kuku-199/Afflatus/HDK/STM32G4/Commander/Commander.pdf

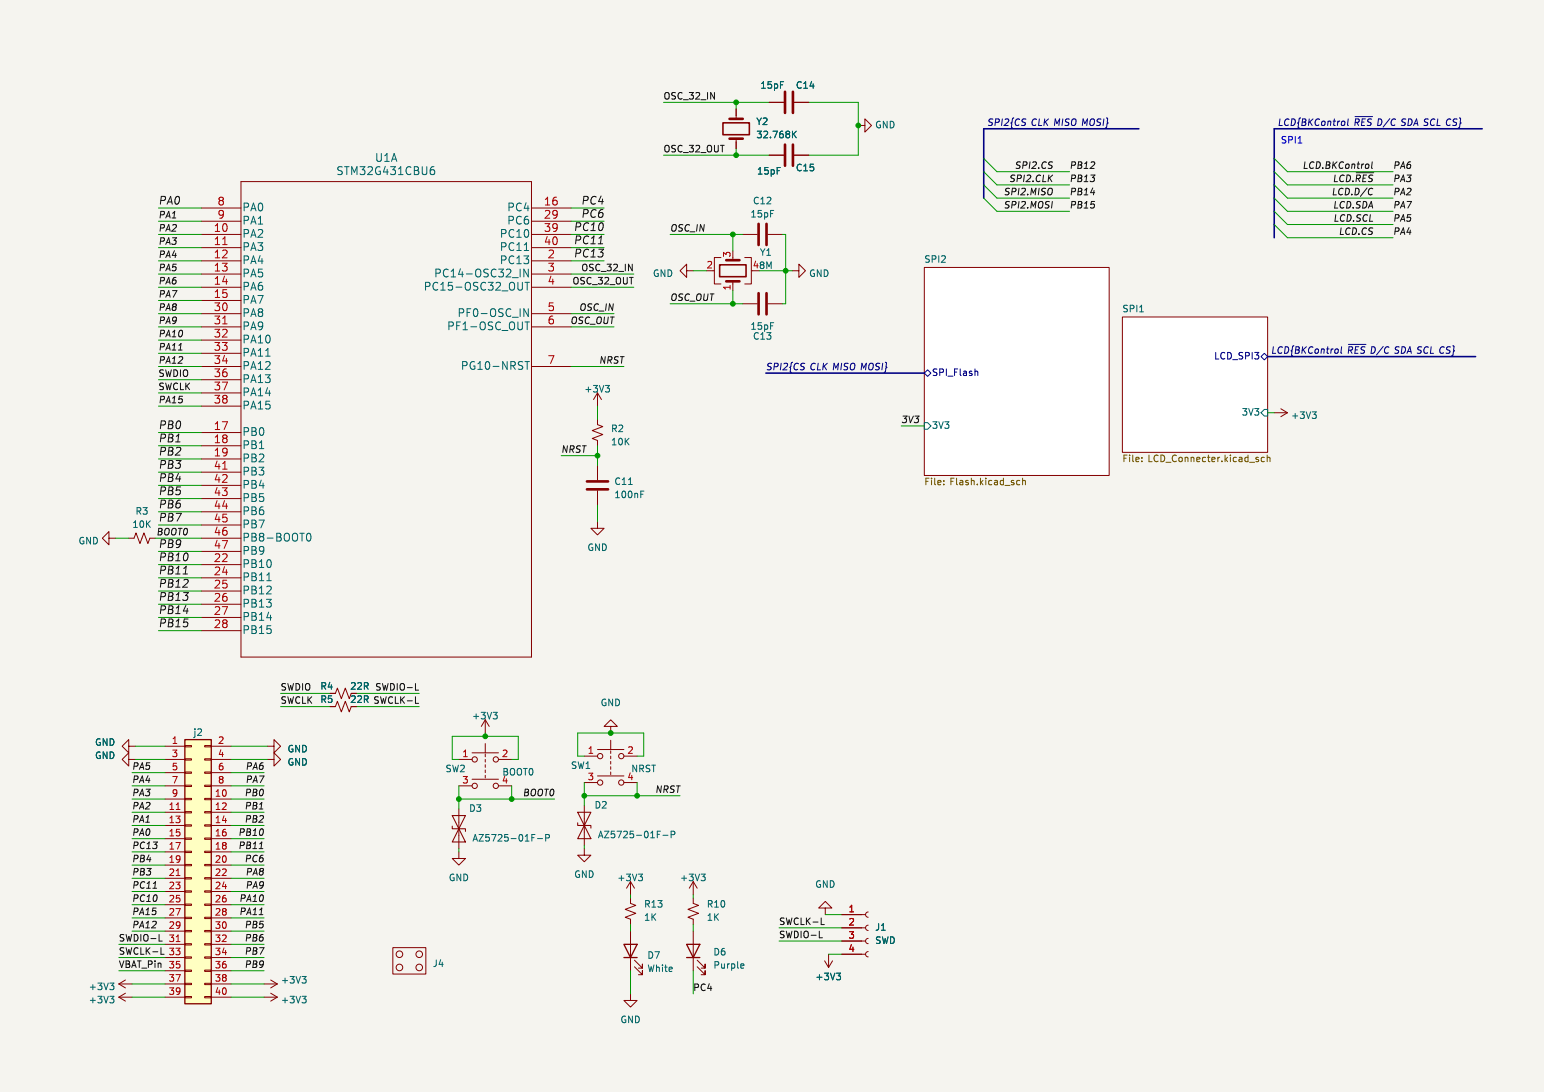
[picture p17: page 1]

LCD{BKControl ~{RES}D/C SDA SCL CS} SWCLK-L

LCD{BKControl ~{RES}D/C SDA SCL CS} PA4 PA5 PA3
SWCLK

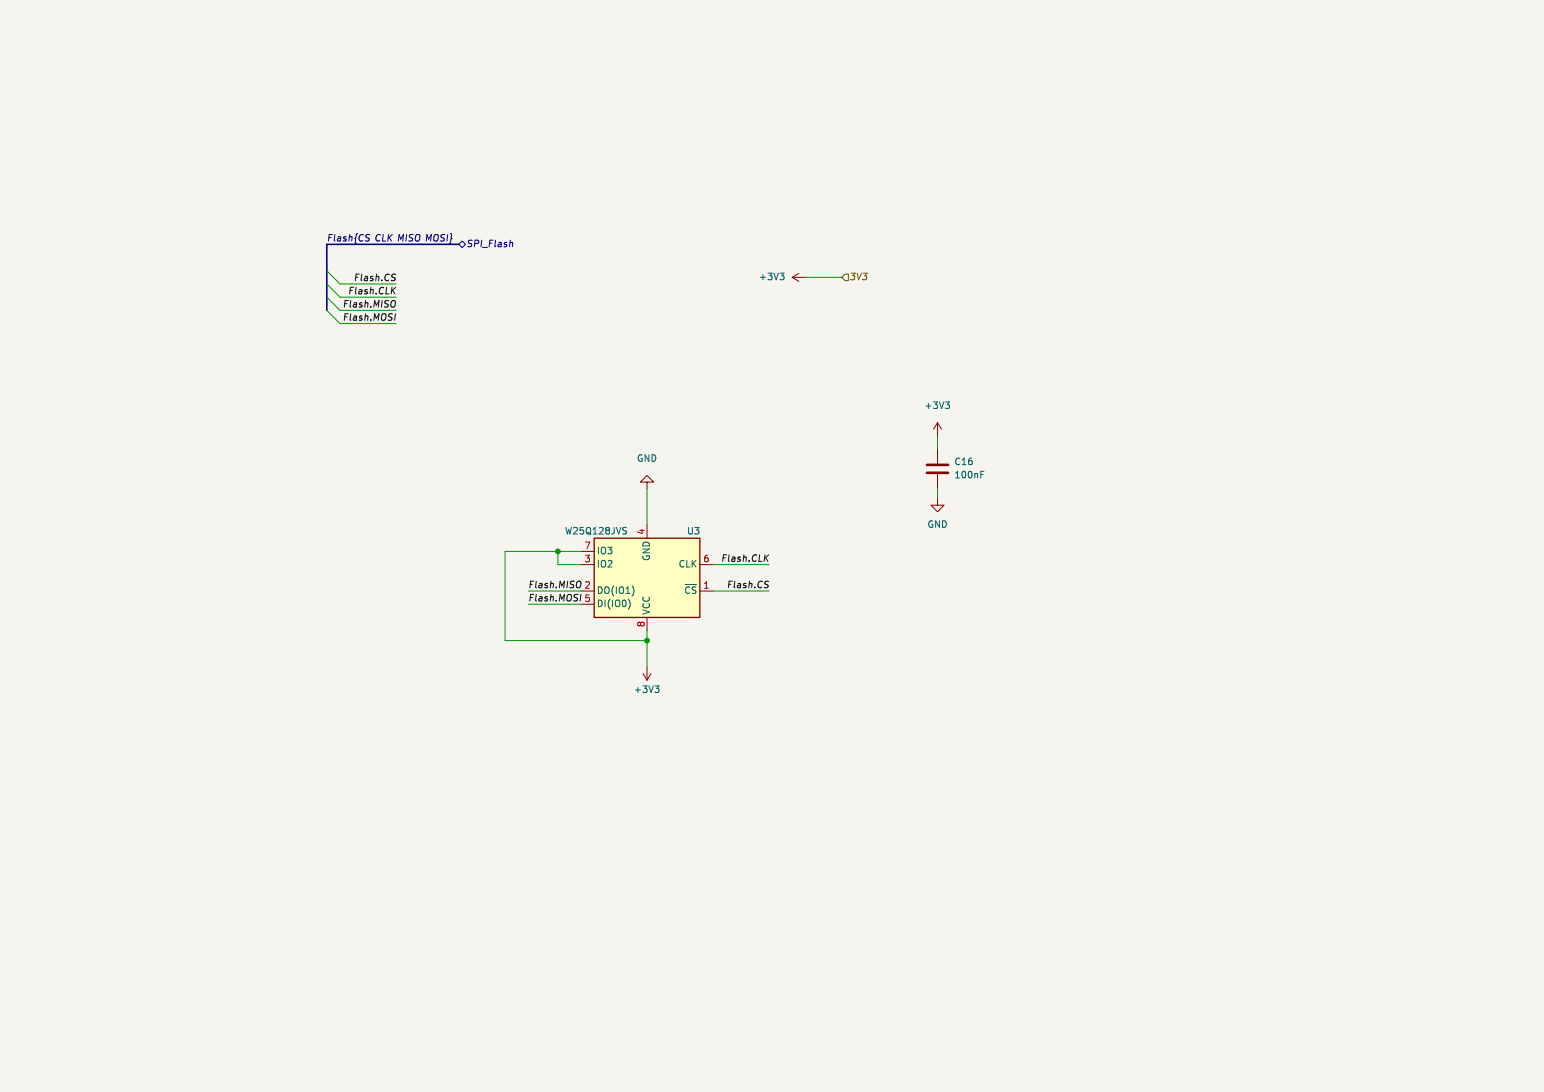
[picture p18: page 2]

Flash{CS CLK MISO MOSI} Flash.MISO

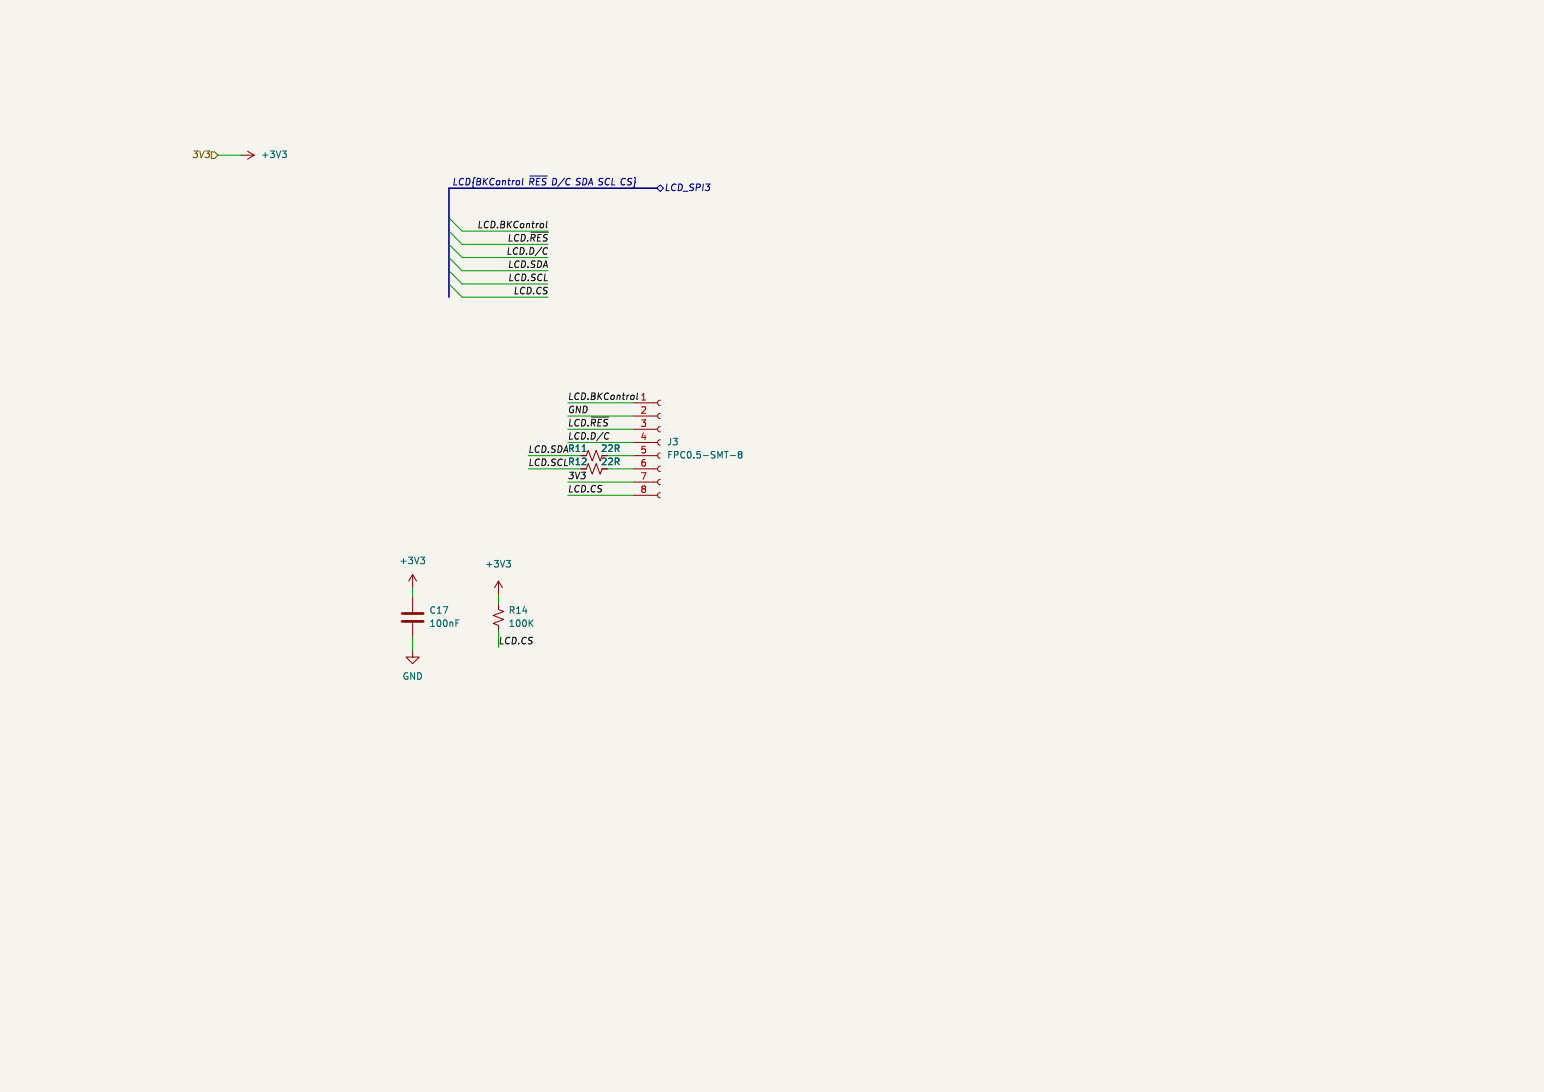
[picture p19: page 3]

LCD.BKControl LCD.SDA
LCD.~{RES} LCD.SCL
LCD.D/C
LCD.SDA
LCD.SCL
LCD.CS

LCD{BKControl ~{RES}D/C SDA SCL CS} LCD.BKControl LCD.D/C GND
