kuku-199/Afflatus/HDK/STM32G4/Expansion/Expansion.pdf

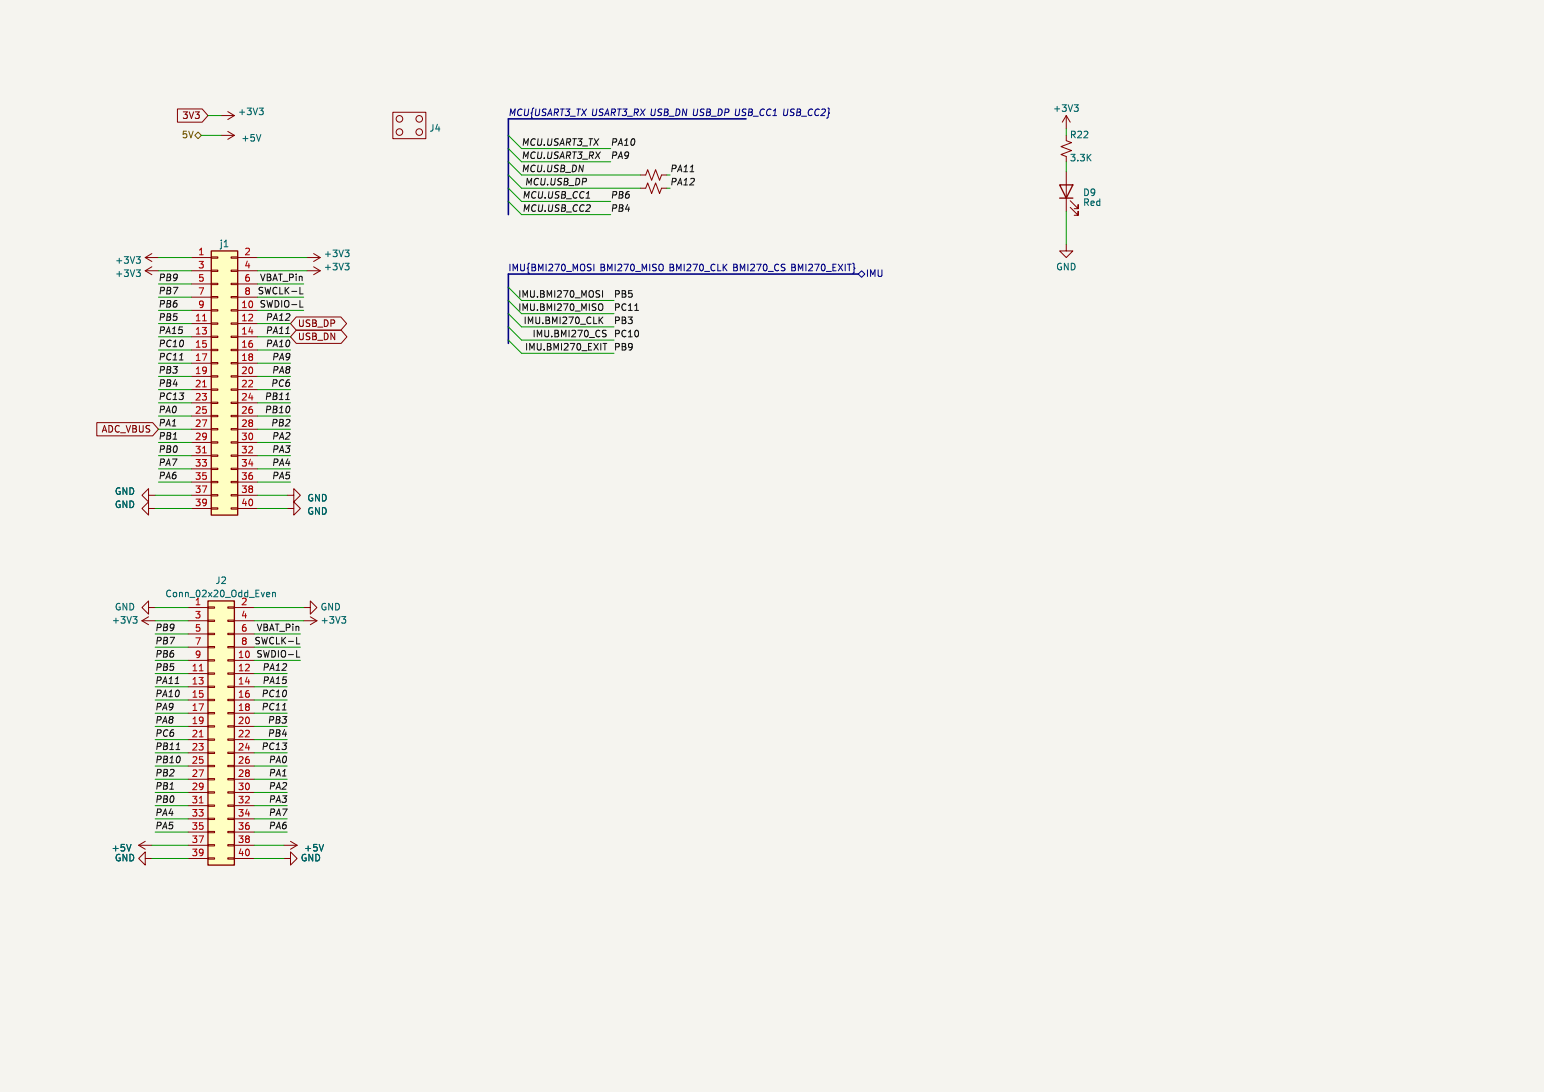
[picture p21: page 1]
